PhoenixRacing/Sensing2017/rtdsensor.ino/rtdsensor.ino.ino

/*************************************************** 
  This is a library for the Adafruit PT100/P1000 RTD Sensor w/MAX31865

  Designed specifically to work with the Adafruit RTD Sensor
  ----> https://www.adafruit.com/products/3328

  This sensor uses SPI to communicate, 4 pins are required to  
  interface
  Adafruit invests time and resources providing this open source code, 
  please support Adafruit and open-source hardware by purchasing 
  products from Adafruit!

  Written by Limor Fried/Ladyada for Adafruit Industries.  
  BSD license, all text above must be included in any redistribution
 ****************************************************/

#include <Adafruit_MAX31865.h>

//#include <Wire.h>
//#include <mcp_can.h>
#include <SPI.h>
// Use software SPI: CS, DI, DO, CLK 
Adafruit_MAX31865 max = Adafruit_MAX31865(8, 11, 12, 13);
// use hardware SPI, just pass in the CS pin
//Adafruit_MAX31865 max = Adafruit_MAX31865(10);

#define DEBUG

// The value of the Rref resistor. Use 430.0 for PT100 and 4300.0 for PT1000
//#define TACH_NODE 2
//#define SPEEDO_NODE 3
//#define PAYLOAD_SIZE 2 // how many bytes to expect from each I2C slave node
//#define NODE_MAX 3 // The highest I2C slave node address to probe
//#define START_NODE 2 // The lowest I2C slave node address to probe

#define RREF      430.0
// The 'nominal' 0-degrees-C resistance of the sensor
// 100.0 for PT100, 1000.0 for PT1000
#define RNOMINAL  100.0

//#define DATA_LEN 4

//MCP_CAN CAN0(10);     // Set CS to pin 10

void setup() {
  Serial.begin(115200);
  Serial.println("Adafruit MAX31865 PT100 Sensor Test!");

  max.begin(MAX31865_3WIRE);  // set to 2WIRE or 4WIRE as necessary

//    if (CAN0.begin(MCP_ANY, CAN_500KBPS, MCP_16MHZ) == CAN_OK) {
//  Serial.println("MCP2515 Initialized Successfully!");
//  }
//  else {
//    Serial.println("Error Initializing MCP2515...");
//  }
}


void loop() {
  uint16_t rtd = max.readRTD();

  Serial.print("RTD value: "); Serial.println(rtd);
  float ratio = rtd;
  ratio /= 32768;
  Serial.print("Ratio = "); Serial.println(ratio,8);
  Serial.print("Resistance = "); Serial.println(RREF*ratio,8);
  Serial.print("Temperature = "); Serial.println(max.temperature(RNOMINAL, RREF));

  // Check and print any faults
  uint8_t fault = max.readFault();
  if (fault) {
    Serial.print("Fault 0x"); Serial.println(fault, HEX);
    if (fault & MAX31865_FAULT_HIGHTHRESH) {
      Serial.println("RTD High Threshold"); 
    }
    if (fault & MAX31865_FAULT_LOWTHRESH) {
      Serial.println("RTD Low Threshold"); 
    }
    if (fault & MAX31865_FAULT_REFINLOW) {
      Serial.println("REFIN- > 0.85 x Bias"); 
    }
    if (fault & MAX31865_FAULT_REFINHIGH) {
      Serial.println("REFIN- < 0.85 x Bias - FORCE- open"); 
    }
    if (fault & MAX31865_FAULT_RTDINLOW) {
      Serial.println("RTDIN- < 0.85 x Bias - FORCE- open"); 
    }
    if (fault & MAX31865_FAULT_OVUV) {
      Serial.println("Under/Over voltage"); 
    }
    max.clearFault();
  }
  Serial.println();
  delay(1000);
}
