PhoenixRacing/Sensing2017/Examples/SD/ReadWrite/ReadWrite.ino

/*
  SD card read/write

 This example shows how to read and write data to and from an SD card file
 The circuit:
 * SD card attached to SPI bus as follows:
 ** MOSI - pin 11
 ** MISO - pin 12
 * 
 ** CLK - pin 13
 ** CS - pin 4 (for MKRZero SD: SDCARD_SS_PIN)

 created   Nov 2010
 by David A. Mellis
 modified 9 Apr 2012
 by Tom Igoe

 This example code is in the public domain.

 */

#include <SPI.h>
#include <SD.h>
#include <Wire.h>
#include "RTClib.h"

RTC_DS3231 rtc;

File myFile;

/* Change these values to set the current initial time */
const byte seconds = 0;
const byte minutes = 0;
const byte hours = 21;

/* Change these values to set the current initial date */
const byte day = 6;
const byte month = 2;
const byte year = 18;

void setup() {
  // Open serial communications and wait for port to open:
  Serial.begin(9600);
  while (!Serial) {
    ; // wait for serial port to connect. Needed for native USB port only

  delay(3000); // wait for console opening

  if (! rtc.begin()) {
    Serial.println("Couldn't find RTC");
    while (1);

    rtc.begin(); // initialize RTC

//  // Set the time
//  rtc.setHours(hours);
//  rtc.setMinutes(minutes);
//  rtc.setSeconds(seconds);
//
//  // Set the date
//  rtc.setDay(day);
//  rtc.setMonth(month);
//  rtc.setYear(year);
  rtc.adjust(DateTime(2018, 2, 6, 21, 0, 0));
  }


  Serial.print("Initializing SD card...");

  if (!SD.begin(4)) {
    Serial.println("initialization failed!");
    return;
  }
  Serial.println("initialization done.");

  // open the file. note that only one file can be open at a time,
  // so you have to close this one before opening another.
  myFile = SD.open("test.txt", FILE_WRITE);

  // if the file opened okay, write to it:
  if (myFile) {
    Serial.print("Writing to test.txt...");
    myFile.println("testing 1, 2, 3.");
    // close the file:
    myFile.close();
    Serial.println("done.");
  } else {
    // if the file didn't open, print an error:
    Serial.println("error opening test.txt");
  }

  // re-open the file for reading:
  myFile = SD.open("test.txt");
  if (myFile) {
    Serial.println("test.txt:");

    // read from the file until there's nothing else in it:
    while (myFile.available()) {
      Serial.write(myFile.read());
    }
    // close the file:
    myFile.close();
  } else {
    // if the file didn't open, print an error:
    Serial.println("error opening test.txt");
  }
}

}
void loop() {

//  // Print date...
//  print2digits(rtc.getDay());
//  Serial.print("/");
//  print2digits(rtc.getMonth());
//  Serial.print("/");
//  print2digits(rtc.getYear());
//  Serial.print(" ");
//
//  // ...and time
//  print2digits(rtc.getHours());
//  Serial.print(":");
//  print2digits(rtc.getMinutes());
//  Serial.print(":");
//  print2digits(rtc.getSeconds());

  DateTime now = rtc.now();

  Serial.print(now.year(), DEC);
  Serial.print('/');
  Serial.print(now.month(), DEC);
  Serial.print('/');
  Serial.print(now.day(), DEC);
  Serial.print(" (");
  Serial.print(daysOfTheWeek[now.dayOfTheWeek()]);
        Serial.print(") ");
        Serial.print(now.hour(), DEC);
        Serial.print(':');
        Serial.print(now.minute(), DEC);
        Serial.print(':');
        Serial.print(now.second(), DEC);
        Serial.println();

  Serial.println();

  delay(1000);

  
  // if the file opened okay, write to it:
  if (myFile) {
    Serial.print("Writing to test.txt...");
    myFile.println(now);
    // close the file:
    myFile.close();
    Serial.println("done.");
  } else {
    // if the file didn't open, print an error:
    Serial.println("error opening test.txt");
  }

  // re-open the file for reading:
  myFile = SD.open("test.txt");
  if (myFile) {
    Serial.println("test.txt:");

    // read from the file until there's nothing else in it:
    while (myFile.available()) {
      Serial.write(myFile.read());
    }
    // close the file:
    myFile.close();
  } else {
    // if the file didn't open, print an error:
    Serial.println("error opening test.txt");
  }
}

  // nothing happens after setup
